CodapopKSP/UntitledSpaceCraft/Documents/Complete_Documentation_Source/PDFs/00_Cover.pdf

## Untitled Space Craft

Complete Documentation
