CodapopKSP/UntitledSpaceCraft/Documents/Complete_Documentation_Source/PDFs/Abort_Stage_Modules.pdf

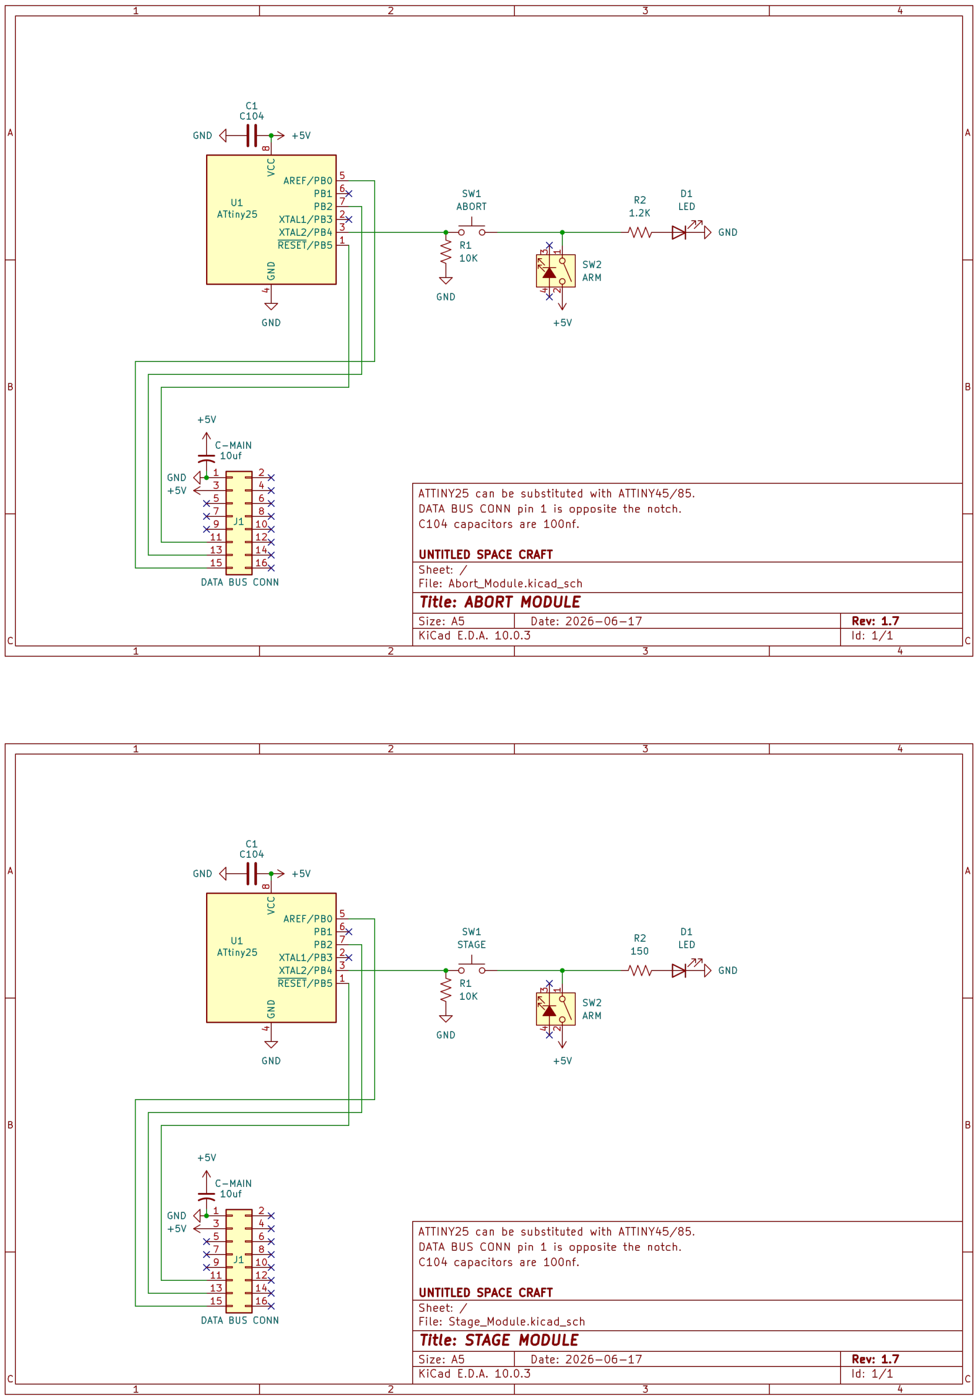
[picture p79: page 1]
