CodapopKSP/UntitledSpaceCraft/Documents/Complete_Documentation_Source/PDFs/Throttle_Executive_Actions_Modules.pdf

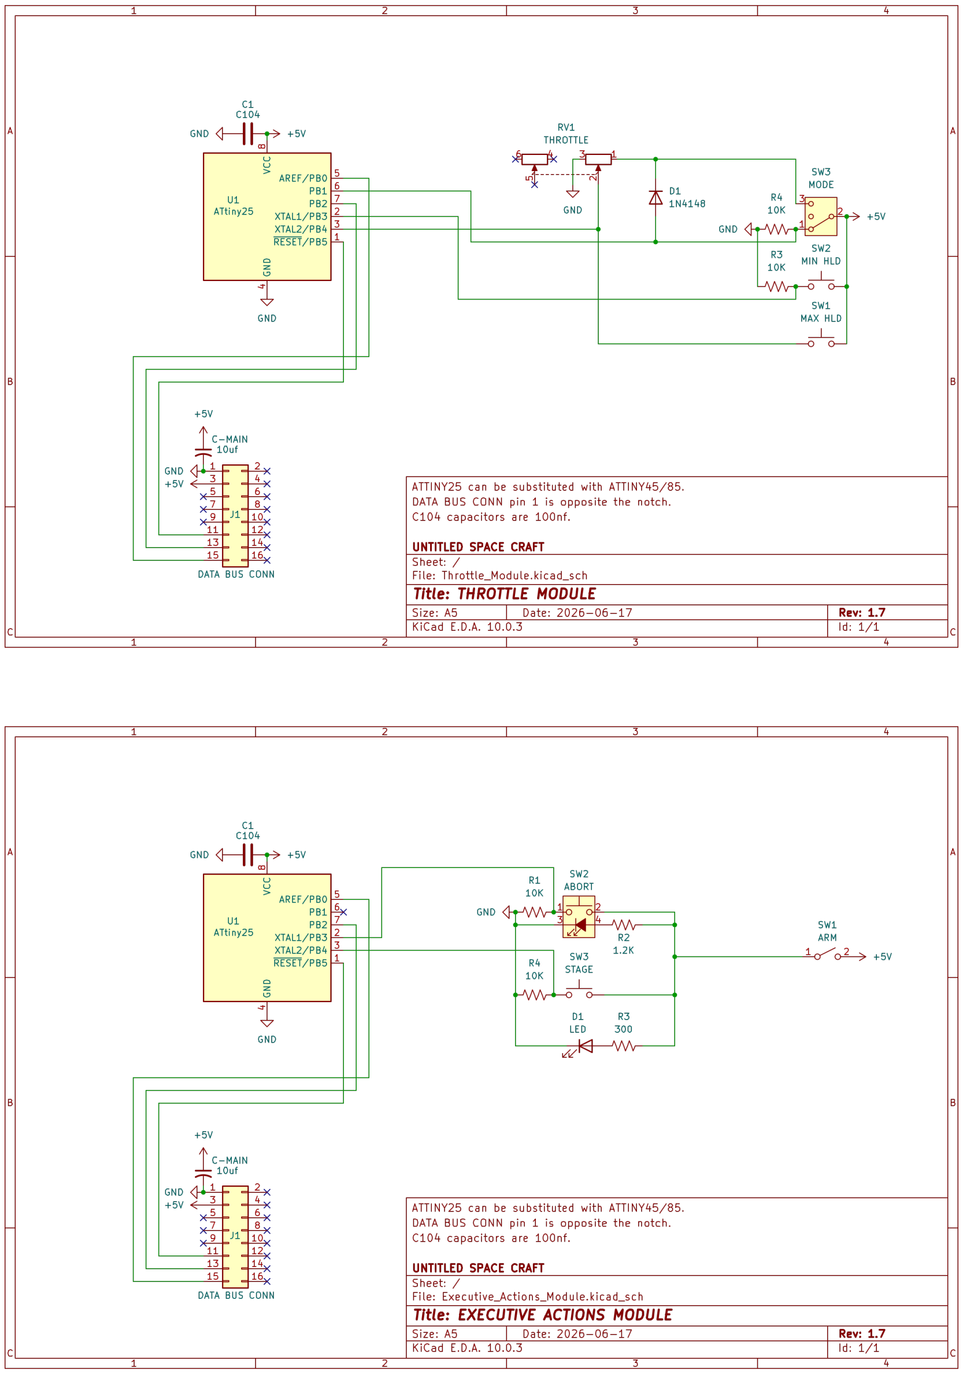
[picture p80: page 1]
