CodapopKSP/UntitledSpaceCraft/Documents/Complete_Documentation_Source/PDFs/Action_Groups_Module.pdf

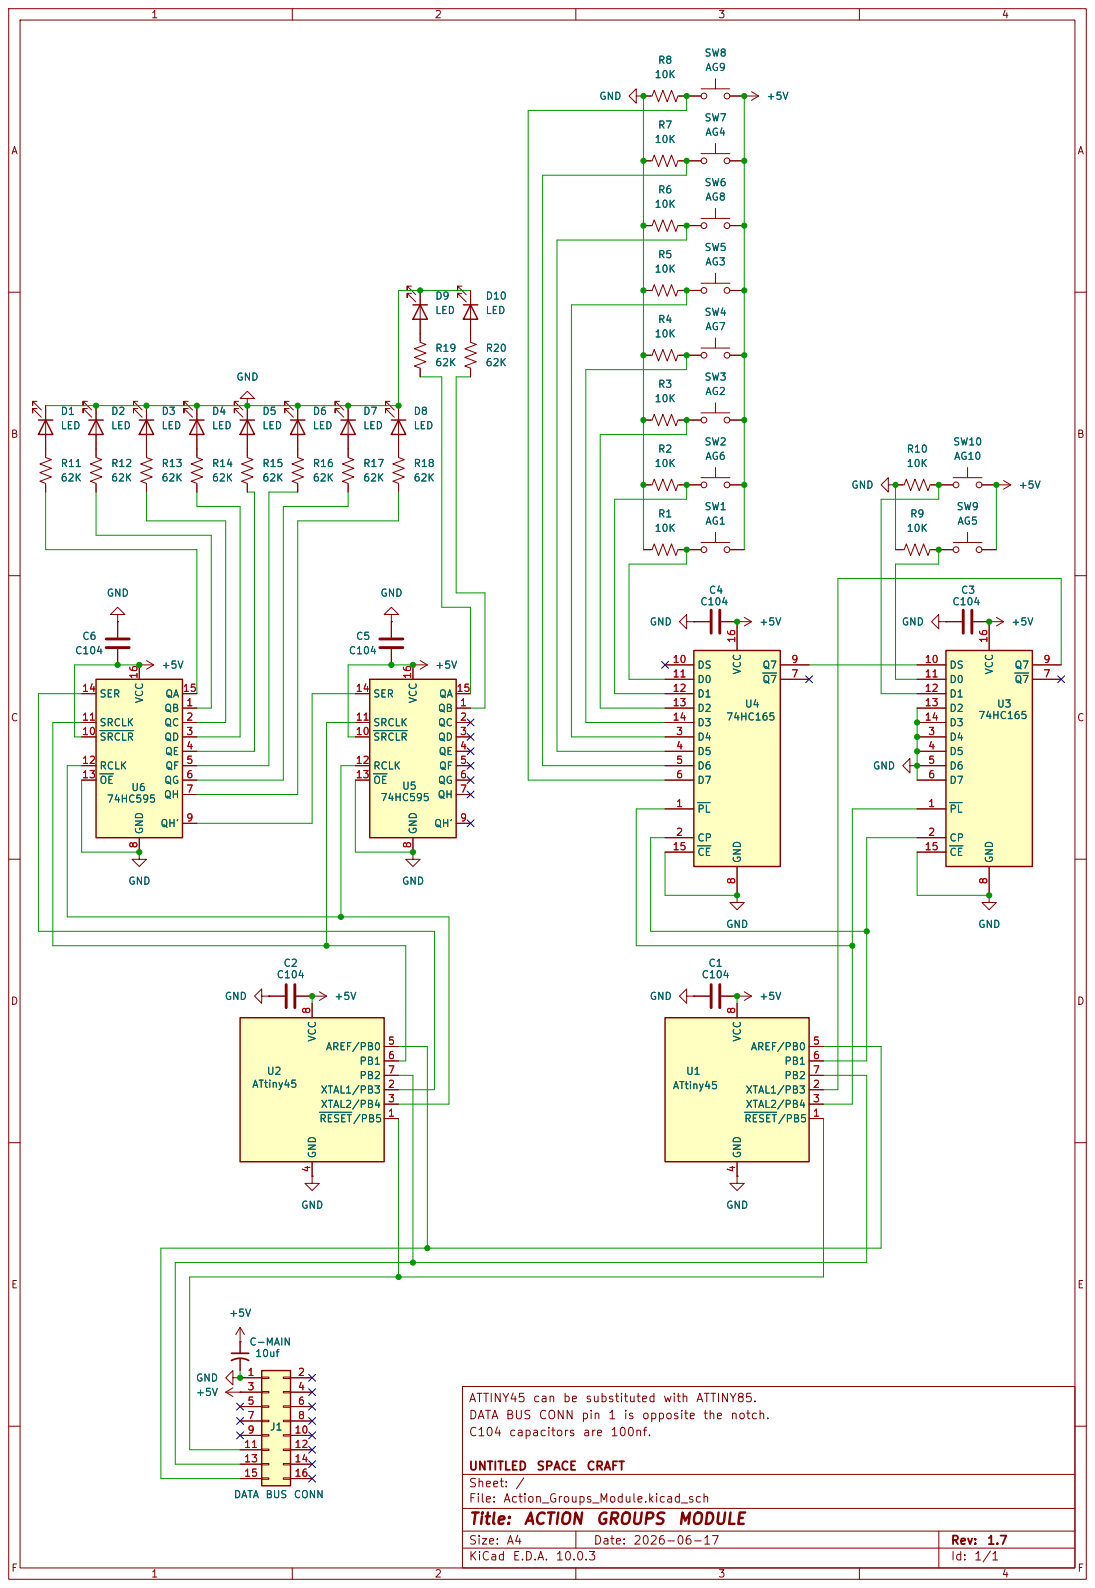
[picture p126: page 1]
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

SRCLR 10 SRCLK 11 RCLK 12 OE 13

DATA BUS CONN pin 1 is opposite the notch.
C104 capacitors are 100nf.

UNTITLED SPACE CRAFT
Sheet: /
File: Action_Groups_Module.kicad_sch
Title: ACTION GROUPS MODULE

Size: A4 | Rev: 1.7 | F Date: 2026-06-17
KiCad E.D.A. 10.0.3 | Id: 1/1
