CodapopKSP/UntitledSpaceCraft/Documents/Complete_Documentation_Source/PDFs/Analog_Module.pdf

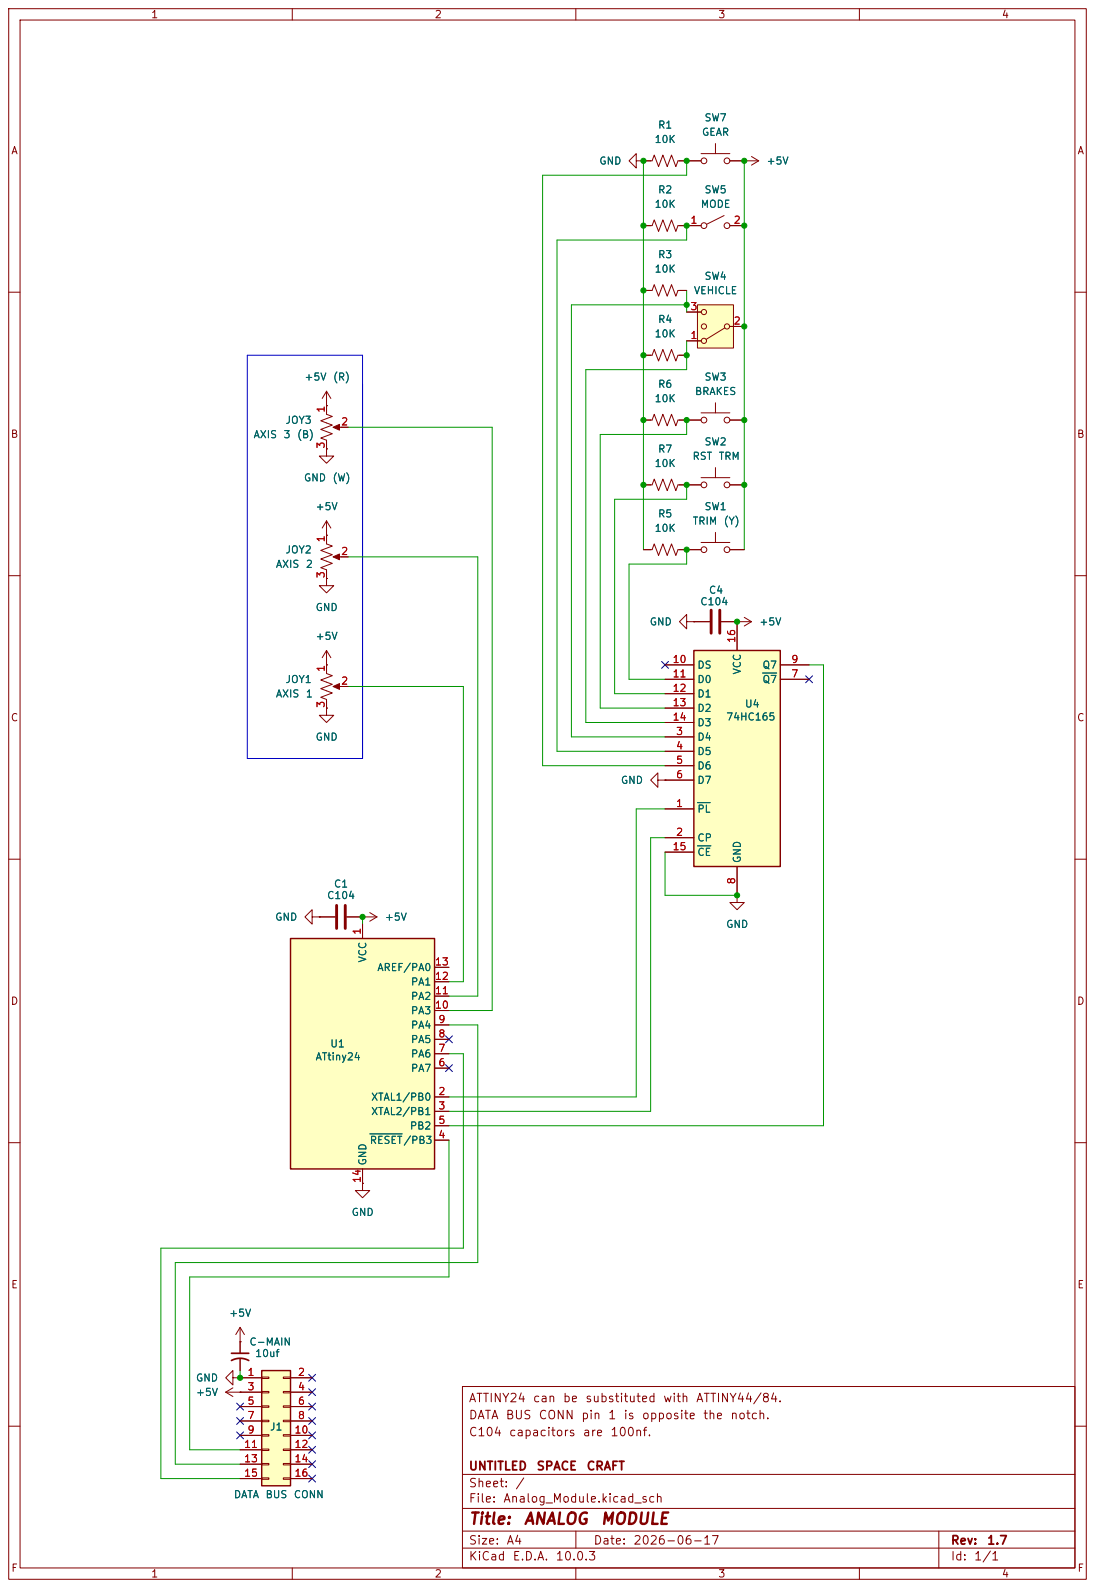
[picture p127: page 1]
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

Size: A4 | Rev: 1.7
KiCad E.D.A. 10.0.3 | Id: 1/1
