CodapopKSP/UntitledSpaceCraft/PCBs/Source/Telemetry_Module/Telemetry_Module.kicad_pcb

## KiCad design PCBs/Source/Telemetry_Module/Telemetry_Module.kicad_pcb (2026-09-23)

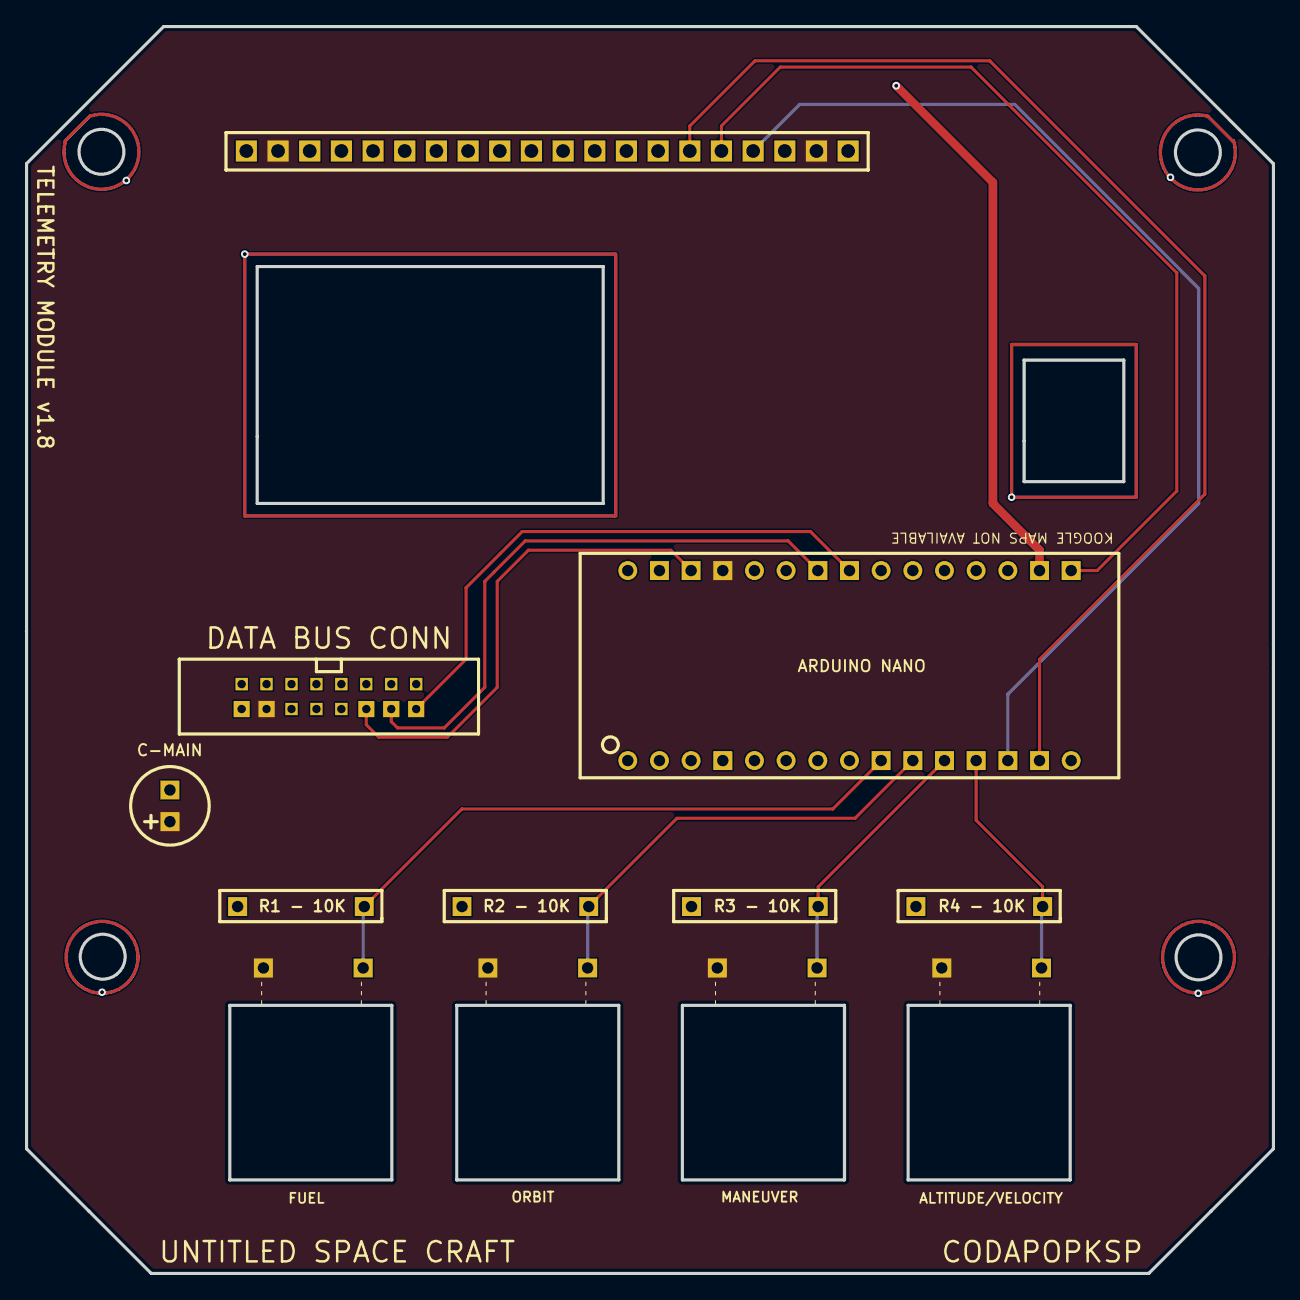
[picture p137: board Telemetry_Module.kicad_pcb from above]

Board: 2 copper layers, 100.0 x 100.0 mm, 51 parts (0 on the bottom side), 12 nets.

Parts:
ARDUINO NANO: Arduino_Nano_Header; DIP-30_L43.18-W15.24-ARDUINONANO
C-MAIN: 10uf; CAP-D6.3×F2.5
NONE1: _
R1, R2, R3, R4: - 10K; TH_RES_10mm
TP_+5V, TP_+5V#2, TP_+5V#3, TP_+5V#4, TP_+5V#5, TP_+5V#6: WirePad
TP_E: WirePad
TP_GND: WirePad
TP_GND#2, TP_GND#3: WirePad
TP_Pad_gge18733, TP_Pad_gge18817, TP_Pad_gge18832, TP_Pad_gge18847, TP_Pad_gge18877, TP_Pad_gge18892, TP_Pad_gge18907, TP_Pad_gge18922, TP_Pad_gge18937, TP_Pad_gge18952, TP_Pad_gge18967, TP_Pad_gge18982: WirePad
TP_RS: WirePad
TP_R_W: WirePad
TP_T1, TP_T2, TP_T3, TP_T4: WirePad
WP1, WP2, WP3, WP4, WP5, WP6, WP7, WP8, WP9, WP10, WP11, WP12, WP13, WP14, WP15, WP16: WPAD-1-30AWG; WPAD-1-PTH-30AWG

Connections:
+5V: ARDUINO NANO.27, C-MAIN.1, TP_+5V.20, TP_+5V#4.17, WP7.1
E: ARDUINO NANO.14, TP_E.30
GND: ARDUINO NANO.4, ARDUINO NANO.29, C-MAIN.2, R1.2, R2.2, R3.2, R4.2, TP_GND.21, TP_GND#2.16, TP_GND#3.21, WP8.1
R/W: ARDUINO NANO.16, TP_R_W.17
RESET: ARDUINO NANO.28, WP3.1
RS: ARDUINO NANO.13, TP_RS.18
SCL: ARDUINO NANO.24, WP2.1
SDA: ARDUINO NANO.23, WP1.1
T1: ARDUINO NANO.9, R1.1
T2: ARDUINO NANO.10, R2.1
T3: ARDUINO NANO.11, R3.1
T4: ARDUINO NANO.12, R4.1
