CodapopKSP/UntitledSpaceCraft/PCBs/Source/Throttle_Module/Throttle_Module.kicad_pcb

## KiCad design PCBs/Source/Throttle_Module/Throttle_Module.kicad_pcb (2026-09-23)

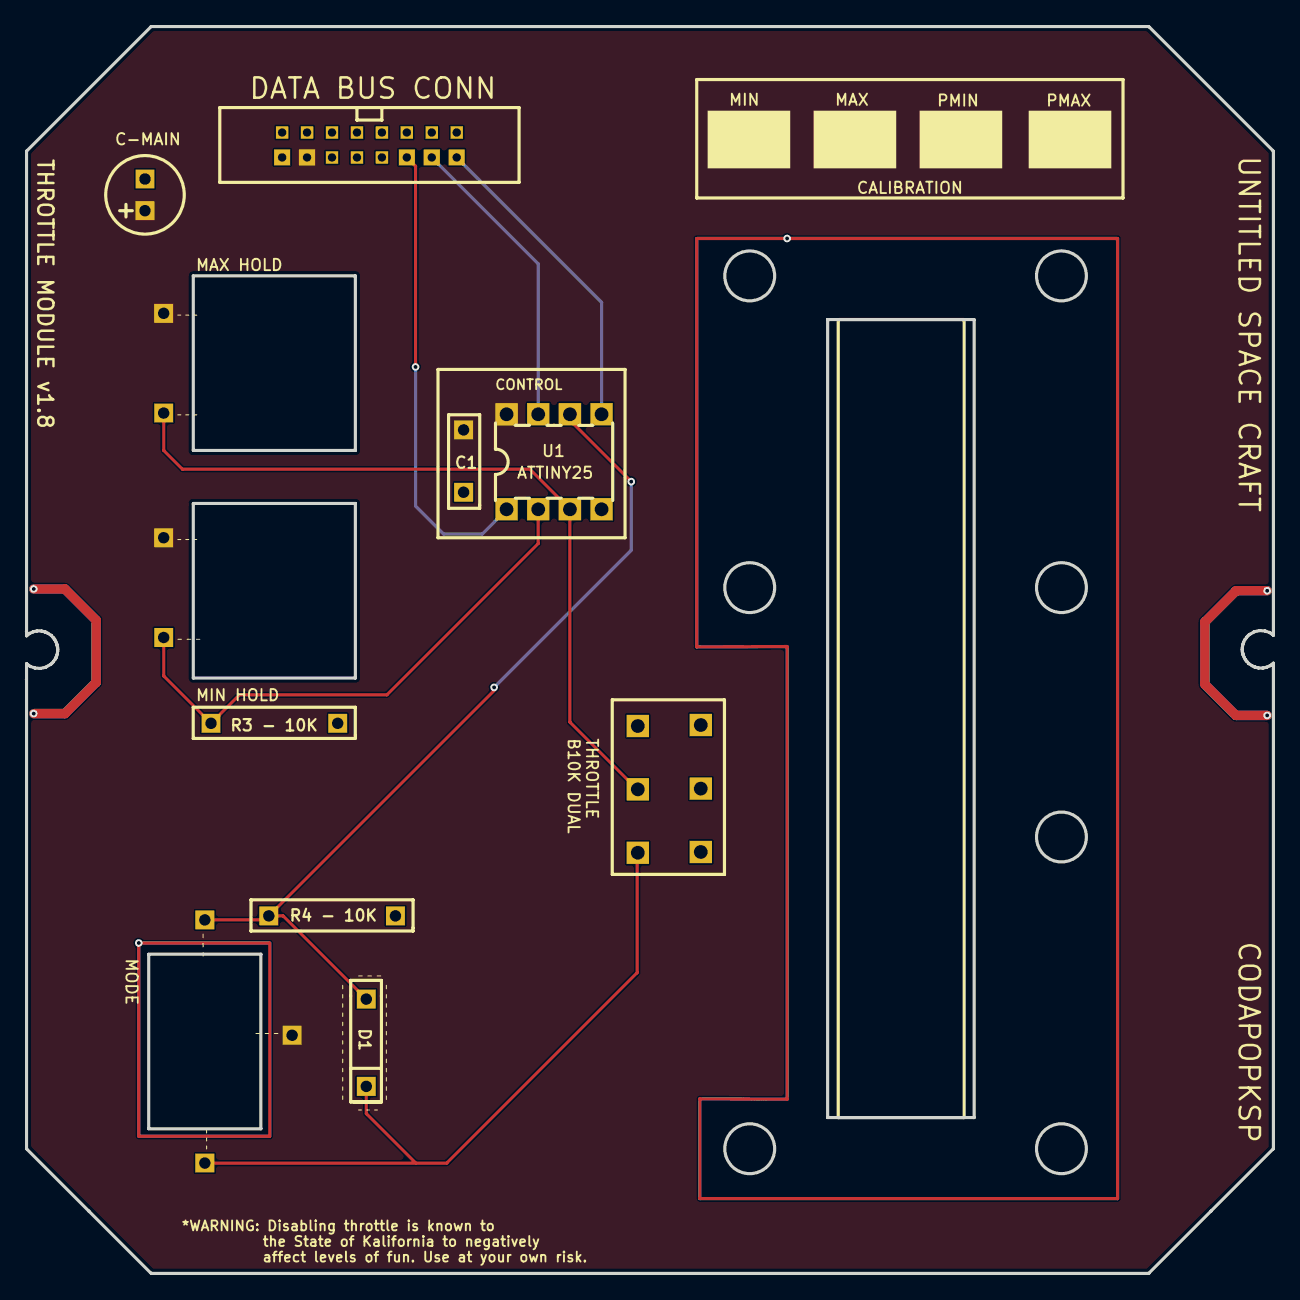
[picture p138: board Throttle_Module.kicad_pcb from above]

Board: 2 copper layers, 100.0 x 100.0 mm, 36 parts (0 on the bottom side), 9 nets.

Parts:
C1: C104; TH_CAP_5mm
C-MAIN: 10uf; CAP-D6.3×F2.5
R3, R4: - 10K; TH_RES_10mm
TP_+5V, TP_+5V#2, TP_+5V#3: WirePad
TP_GND: WirePad
TP_MINHOLD: WirePad
TP_PCONT: WirePad
TP_PCONT#2: WirePad
TP_POWER: WirePad
TP_POWER#2, TP_POWER#3: WirePad
TP_Pad_gge22046, TP_Pad_gge22136, TP_Pad_gge22247: WirePad
TP_THROTTLE: WirePad
TP_THROTTLE#2: WirePad
U1: ATtiny25; PDIP-8_L9.3-W6.4-P2.54-LS7.6-BL
WP54, WP55, WP56, WP57, WP58, WP59, WP60, WP61, WP62, WP63, WP64, WP65, WP66, WP67, WP68, WP69: WPAD-1-30AWG; WPAD-1-PTH-30AWG

Connections:
+5V: C1.2, C-MAIN.1, TP_+5V.1, TP_+5V#2.1, TP_+5V#3.1, U1.8, WP61.1
GND: C1.1, C-MAIN.2, R3.1, R4.1, TP_GND.3, U1.4, WP62.1
MINHOLD: R3.2, TP_MINHOLD.1, U1.2
PCONT: R4.2, TP_PCONT.5, TP_PCONT#2.1, U1.6
POWER: TP_POWER.1, TP_POWER#2.4, TP_POWER#3.4
RESET: U1.1, WP57.1
SCL: U1.7, WP56.1
SDA: U1.5, WP55.1
THROTTLE: TP_THROTTLE.2, TP_THROTTLE#2.1, U1.3
