CodapopKSP/UntitledSpaceCraft/PCBs/Source/Quad_Hub/Quad_Hub.kicad_pcb

## KiCad design PCBs/Source/Quad_Hub/Quad_Hub.kicad_pcb (2026-09-23)

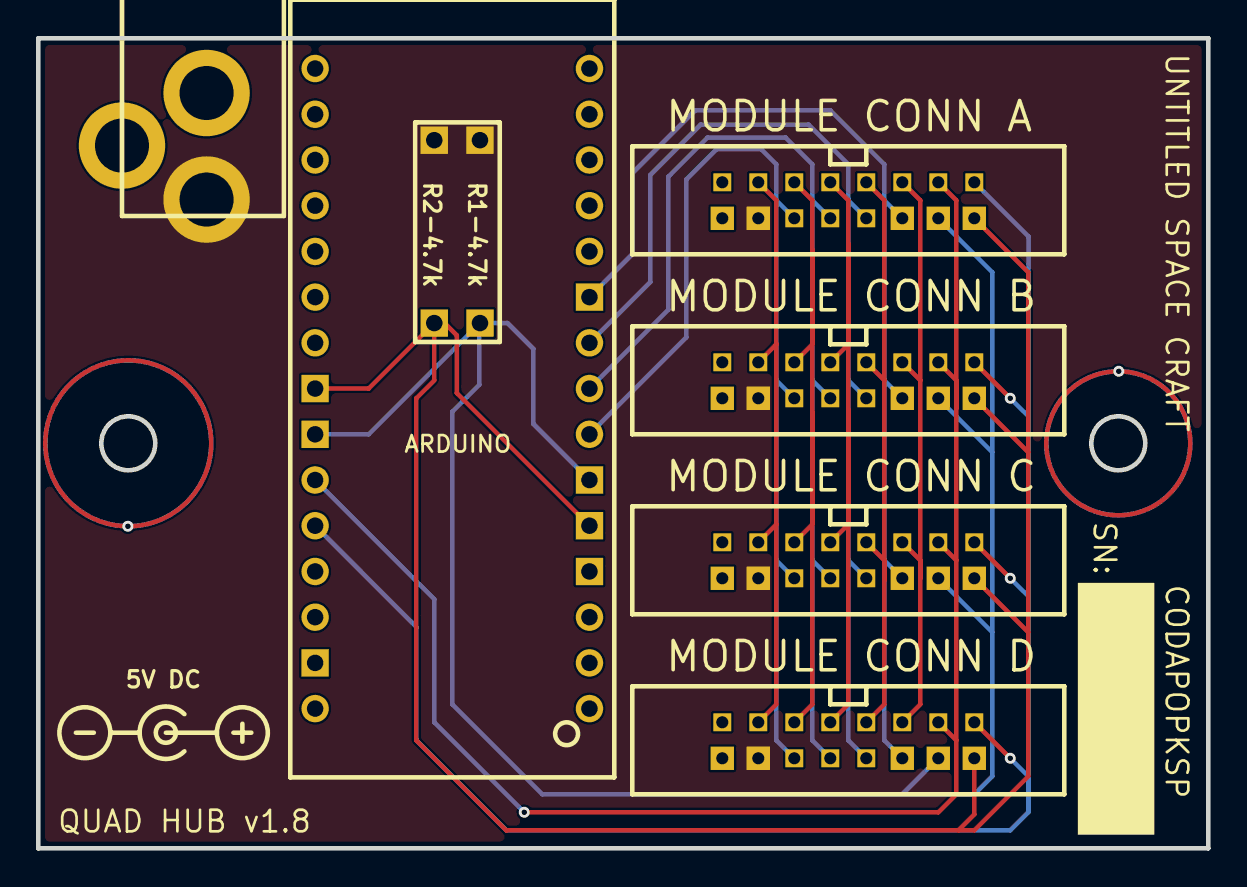
[picture p139: board Quad_Hub.kicad_pcb from above]

Board: 2 copper layers, 65.0 x 45.0 mm, 68 parts (0 on the bottom side), 15 nets.

Parts:
ARDUINO: Arduino_Nano_Header; DIP-30_L43.18-W15.24-ARDUINONANO
NONE: _
NONEAWD: _
U1: PJ-102A
WP17, WP18, WP19, WP20, WP21, WP22, WP23, WP24, WP25, WP26, WP27, WP28, WP29, WP30, WP31, WP32, WP33, WP34, WP35, WP36, WP37, WP38, WP39, WP40, WP41, WP42, WP43, WP44, WP45, WP46, WP47, WP48, WP49, WP50, WP51, WP52, WP53, WP54, WP55, WP56, WP57, WP58, WP59, WP60, WP61, WP62, WP63, WP64, WP65, WP66, WP67, WP68, WP69, WP70, WP71, WP72, WP73, WP74, WP75, WP76, WP77, WP78, WP79, WP80: WPAD-1-30AWG; WPAD-1-PTH-30AWG

Connections:
+5V: NONE.2, NONE.4, U1.TIP, WP24.1, WP41.1, WP57.1, WP73.1
ANALOG0: WP20.1, WP45.1, WP61.1, WP77.1
ANALOG1: WP19.1, WP46.1, WP62.1, WP78.1
ANALOG2: WP18.1, WP47.1, WP63.1, WP79.1
ANALOG3: WP32.1, WP33.1, WP49.1, WP65.1
ANALOG4: ARDUINO.25, WP31.1, WP34.1, WP50.1, WP66.1
ANALOG5: ARDUINO.26, WP17.1, WP48.1, WP64.1, WP80.1
DIGITAL1: WP21.1, WP44.1, WP60.1, WP76.1
DIGITAL2: ARDUINO.7, WP25.1, WP40.1, WP56.1, WP72.1
DIGITAL3: ARDUINO.8, WP26.1, WP39.1, WP55.1, WP71.1
DIGITAL4: ARDUINO.9, WP27.1, WP38.1, WP54.1, WP70.1
GND: ARDUINO.4, ARDUINO.29, U1.RING, WP23.1, WP42.1, WP58.1, WP74.1
RESET: ARDUINO.10, WP28.1, WP37.1, WP53.1, WP69.1
SCL: ARDUINO.6, ARDUINO.24, NONE.5, WP29.1, WP36.1, WP52.1, WP68.1
SDA: ARDUINO.5, ARDUINO.23, NONE.3, WP30.1, WP35.1, WP51.1, WP67.1
