CodapopKSP/UntitledSpaceCraft/Firmware/Container Firmware/Module-Specific/Action Groups/Hub_Action_Groups/01_System_Functions.ino

//|-------------------------------|
//|       System Functions        |
//|-------------------------------|

void registerMessageChannels() {
  mySimpit.inboundHandler(messageHandler);
  mySimpit.registerChannel(CAGSTATUS_MESSAGE);
}

byte sendHandshake(int address) {
  Wire.requestFrom(address, 1);
  byte connection = Wire.read();
  return connection;
}

void checkConnections() {
  Action_Ctrl_Con = (sendHandshake(Action_Ctrl_)!=255);
}

void transmissions() {
  //ctrl_address, dspl_address, in_bytes, out_bytes, ctrl[], dspl[]
  if (Action_Ctrl_Con) {module_transmission(Action_Ctrl_, Action_Dspl_, 2, 2, Action_Ctrl, Action_Dspl, AG_Update);}
}

void actions() {
  if (Action_Ctrl_Con){Action_Action();}
}
