CodapopKSP/UntitledSpaceCraft/Firmware/Container Firmware/Module-Specific/Action Groups/Hub_Action_Groups/02_Transmissions.ino

//|-------------------|
//|   Transmissions   |
//|-------------------|

void module_transmission(int ctrl_address, int dspl_address, int in_bytes, int out_bytes, byte ctrl[], byte dspl[], bool &UpdateFlag) {
  // Control
  if (ctrl_address != 0) {
    Wire.requestFrom(ctrl_address, in_bytes);
    for (int i = 0; i < in_bytes; i++) {
      ctrl[i] = Wire.read();
    }
  }

  // Display
  if ((dspl_address != 0) and (UpdateFlag)) {
    UpdateFlag = false;
    Wire.beginTransmission(dspl_address);
    for (int i = 0; i < out_bytes; i++) {
      Wire.write(dspl[i]);
    }
    Wire.endTransmission();
    mySimpit.printToKSP("Display Complete", PRINT_TO_SCREEN);
  }
}

void messageHandler(byte messageType, byte msg[], byte msgSize) {
  switch(messageType) {
    case CAGSTATUS_MESSAGE:
      if (msgSize == sizeof(cagStatusMessage)) {
        cagStatusMessage myAG;
        myAG = parseCAGStatusMessage(msg);
        bool Action_Dspl_b[10] = {};
        for (int i = 0; i < 10; i++) {
          Action_Dspl_b[i] = (myAG.is_action_activated(AG_List[i]));
        }
        for (int i = 0; i < 8; i++) {
          bitWrite(Action_Dspl[0], i, Action_Dspl_b[i]);
        }
        for (int i = 0; i < 2; i++) {
          bitWrite(Action_Dspl[1], i, Action_Dspl_b[i+8]);
        }
      }
      AG_Update = true;
      mySimpit.printToKSP("Message Complete", PRINT_TO_SCREEN);
      break;
  }
}
