CodapopKSP/UntitledSpaceCraft/Firmware/Container Firmware/Module-Specific/Action Groups/Hub_Action_Groups_23/actionResults.h

//|-------------------|
//|      Results      |
//|-------------------|

  const int AG_List[10] = {1,6,2,7,3,8,4,9,5,10};
  const int AG2_List[10] = {11,16,12,17,13,18,14,19,15,20};
  const int AG3_List[10] = {21,26,22,27,23,28,24,29,25,30};
