CodapopKSP/UntitledSpaceCraft/Firmware/Container Firmware/Module-Specific/Analog Controls/Hub_Analog/01_System_Functions.ino

//|-------------------------------|
//|       System Functions        |
//|-------------------------------|

void registerMessageChannels() {
  mySimpit.inboundHandler(messageHandler);
  mySimpit.registerChannel(ACTIONSTATUS_MESSAGE);
}

byte sendHandshake(int address) {
  Wire.requestFrom(address, 1);
  byte connection = Wire.read();
  return connection;
}

void checkConnections() {
  Analog_Con = (sendHandshake(Analog_)!=255);
}

void transmissions() {
  //ctrl_address, dspl_address, in_bytes, out_bytes, ctrl[], dspl[]
  if (Analog_Con) {module_transmission(Analog_, 0, 8, 0, Analog, 0);}
}

void actions() {
  if (Analog_Con){Analog_Action();}
}
