CodapopKSP/UntitledSpaceCraft/Firmware/Container Firmware/Module-Specific/Analog Controls/Hub_Rotation_Throttle/01_System_Functions.ino

//|-------------------------------|
//|       System Functions        |
//|-------------------------------|

byte sendHandshake(int address) {
  Wire.requestFrom(address, 1);
  byte connection = Wire.read();
  return connection;
}

void checkConnections() {
  Rotation_Con = (sendHandshake(Rotation_)!=255);
}

void transmissions() {
  //ctrl_address, dspl_address, in_bytes, out_bytes, ctrl[], dspl[]
  if (Rotation_Con) {module_transmission(Rotation_, 0, 9, 0, Rotation, 0);}
}

void actions() {
  if (Rotation_Con){Rotation_Action();}
}
