CodapopKSP/UntitledSpaceCraft/Firmware/Container Firmware/Module-Specific/Executive Actions/Hub_Executive_Actions_Control/02_Transmissions.ino

//|-------------------|
//|   Transmissions   |
//|-------------------|

void module_transmission(int ctrl_address, int dspl_address, int in_bytes, int out_bytes, byte ctrl[], byte dspl[], bool &UpdateFlag) {
  mySimpit.printToKSP(String(dspl[0]), PRINT_TO_SCREEN);
  // Control
  if (ctrl_address != 0) {
    Wire.requestFrom(ctrl_address, in_bytes);
    for (int i = 0; i < in_bytes; i++) {
      ctrl[i] = Wire.read();
    }
  }
  /*
  // Display
  if ((dspl_address != 0) and (UpdateFlag)) {
    Wire.beginTransmission(dspl_address);
    for (int i = 0; i < out_bytes; i++) {
      Wire.write(dspl[i]);
    }
    Wire.endTransmission();
  }*/
}

void messageHandler(byte messageType, byte msg[], byte msgSize) {
  switch(messageType) {
    case SAS_MODE_INFO_MESSAGE:
      if (msgSize == sizeof(SASInfoMessage)) {
        SASInfoMessage mySAS;
        mySAS = parseSASInfoMessage(msg);
        bool stabAssist = (mySAS.currentSASMode==AP_STABILITYASSIST);
        bitWrite(EA_Control_Dspl[0], 3, stabAssist);
      }
      break;

    case ACTIONSTATUS_MESSAGE:
      if (msgSize == 1) {
        currentActionStatus = msg[0];
        bitWrite(EA_Control_Dspl[0], 0, currentActionStatus & LIGHT_ACTION);
        bitWrite(EA_Control_Dspl[0], 2, currentActionStatus & GEAR_ACTION);
        bitWrite(EA_Control_Dspl[0], 4, currentActionStatus & SAS_ACTION);
        bitWrite(EA_Control_Dspl[0], 5, currentActionStatus & RCS_ACTION);
      }
      break;
  }
}
