CodapopKSP/UntitledSpaceCraft/Firmware/Container Firmware/Module-Specific/Hub_Camera/actionResults.h

//|-------------------|
//|      Results      |
//|-------------------|

  const int Camera_List[10] = {
    0x71, // F2
    0x70, // F1
    0x6D, // -
    0x27, // RIGHT
    0x28, // DOWN
    0x26, // UP
    0x25, // LEFT
    0x6B, // +
    0x43, // C
    0x56, // V
  };
