CodapopKSP/UntitledSpaceCraft/Firmware/Container Firmware/Module-Specific/Hub_EVA/actionResults.h

//|-------------------|
//|      Results      |
//|-------------------|

const int EVA_List[11] = {
    0x42, // B
    0x46, // F
    0x20, // SPACE
    0x52, // R
    0x10, // SHIFT
    0xA2, // CTRL
    0x57, // W
    0x41, // A
    0x53, // S
    0x44, // D
    0x55  // U
  };
