CodapopKSP/UntitledSpaceCraft/Firmware/Container Firmware/Module-Specific/Hub_Time/actionResults.h

//|-------------------|
//|      Results      |
//|-------------------|

const int Time_List[8] = {
    0x12, // ALT
    0,    // NULL
    0xBE, // .
    0xBC, // ,
    0xBF, // /
    0x1B, // ESC
    0x74, // F5
    0x78, // F9
  };
