CodapopKSP/UntitledSpaceCraft/Firmware/Container Firmware/Module-Specific/Navigation/Hub_Navigation/actionResults.h

//|-------------------|
//|      Results      |
//|-------------------|

const int Nav_List[8] = {
    0xC0, // `
    0xDB, // [
    0,    // NULL
    0xDD, // ]
    0x9,  // TAB
    0,    // NULL
    0x4D, // M
    0x6E, // .
  };
