CodapopKSP/UntitledSpaceCraft/Firmware/Container Firmware/Module-Specific/Navigation/Hub_Navigation_Time/actionResults.h

//|-------------------|
//|      Results      |
//|-------------------|

const int Navigation_Time_List[8] = {
    0x12, // ALT
    0x1B, // ESC
    0xBE, // .
    0xBC, // ,
    0xBF, // /
    0xDD, // ]
    0xC0, // `
    0x4D, // M
  };
