CodapopKSP/UntitledSpaceCraft/Firmware/Container Firmware/Module-Specific/Hub_Utility_Navigation/actionResults.h

//|-------------------|
//|      Results      |
//|-------------------|

const int Util_Nav_List[11] = {
    0x42, // B
    0x46, // F
    0x20, // SPACE
    0x52, // R
    0x55, // U
    0xDD, // ]
    0,    // NULL
    0x4D, // M
  };
