CodapopKSP/UntitledSpaceCraft/Firmware/Container Firmware/Module-Specific/Hub_Utility_Time/actionResults.h

//|-------------------|
//|      Results      |
//|-------------------|

const int Util_Time_List[11] = {
    0x42, // B
    0x46, // F
    0x20, // SPACE
    0x52, // R
    0x55, // U
    0x78, // F9
    0x74, // F5
    0x1B, // ESC
  };
